Picatout/transistor-tester/transistor-tester.sch

## KiCad design transistor-tester.sch (2013-03-15)

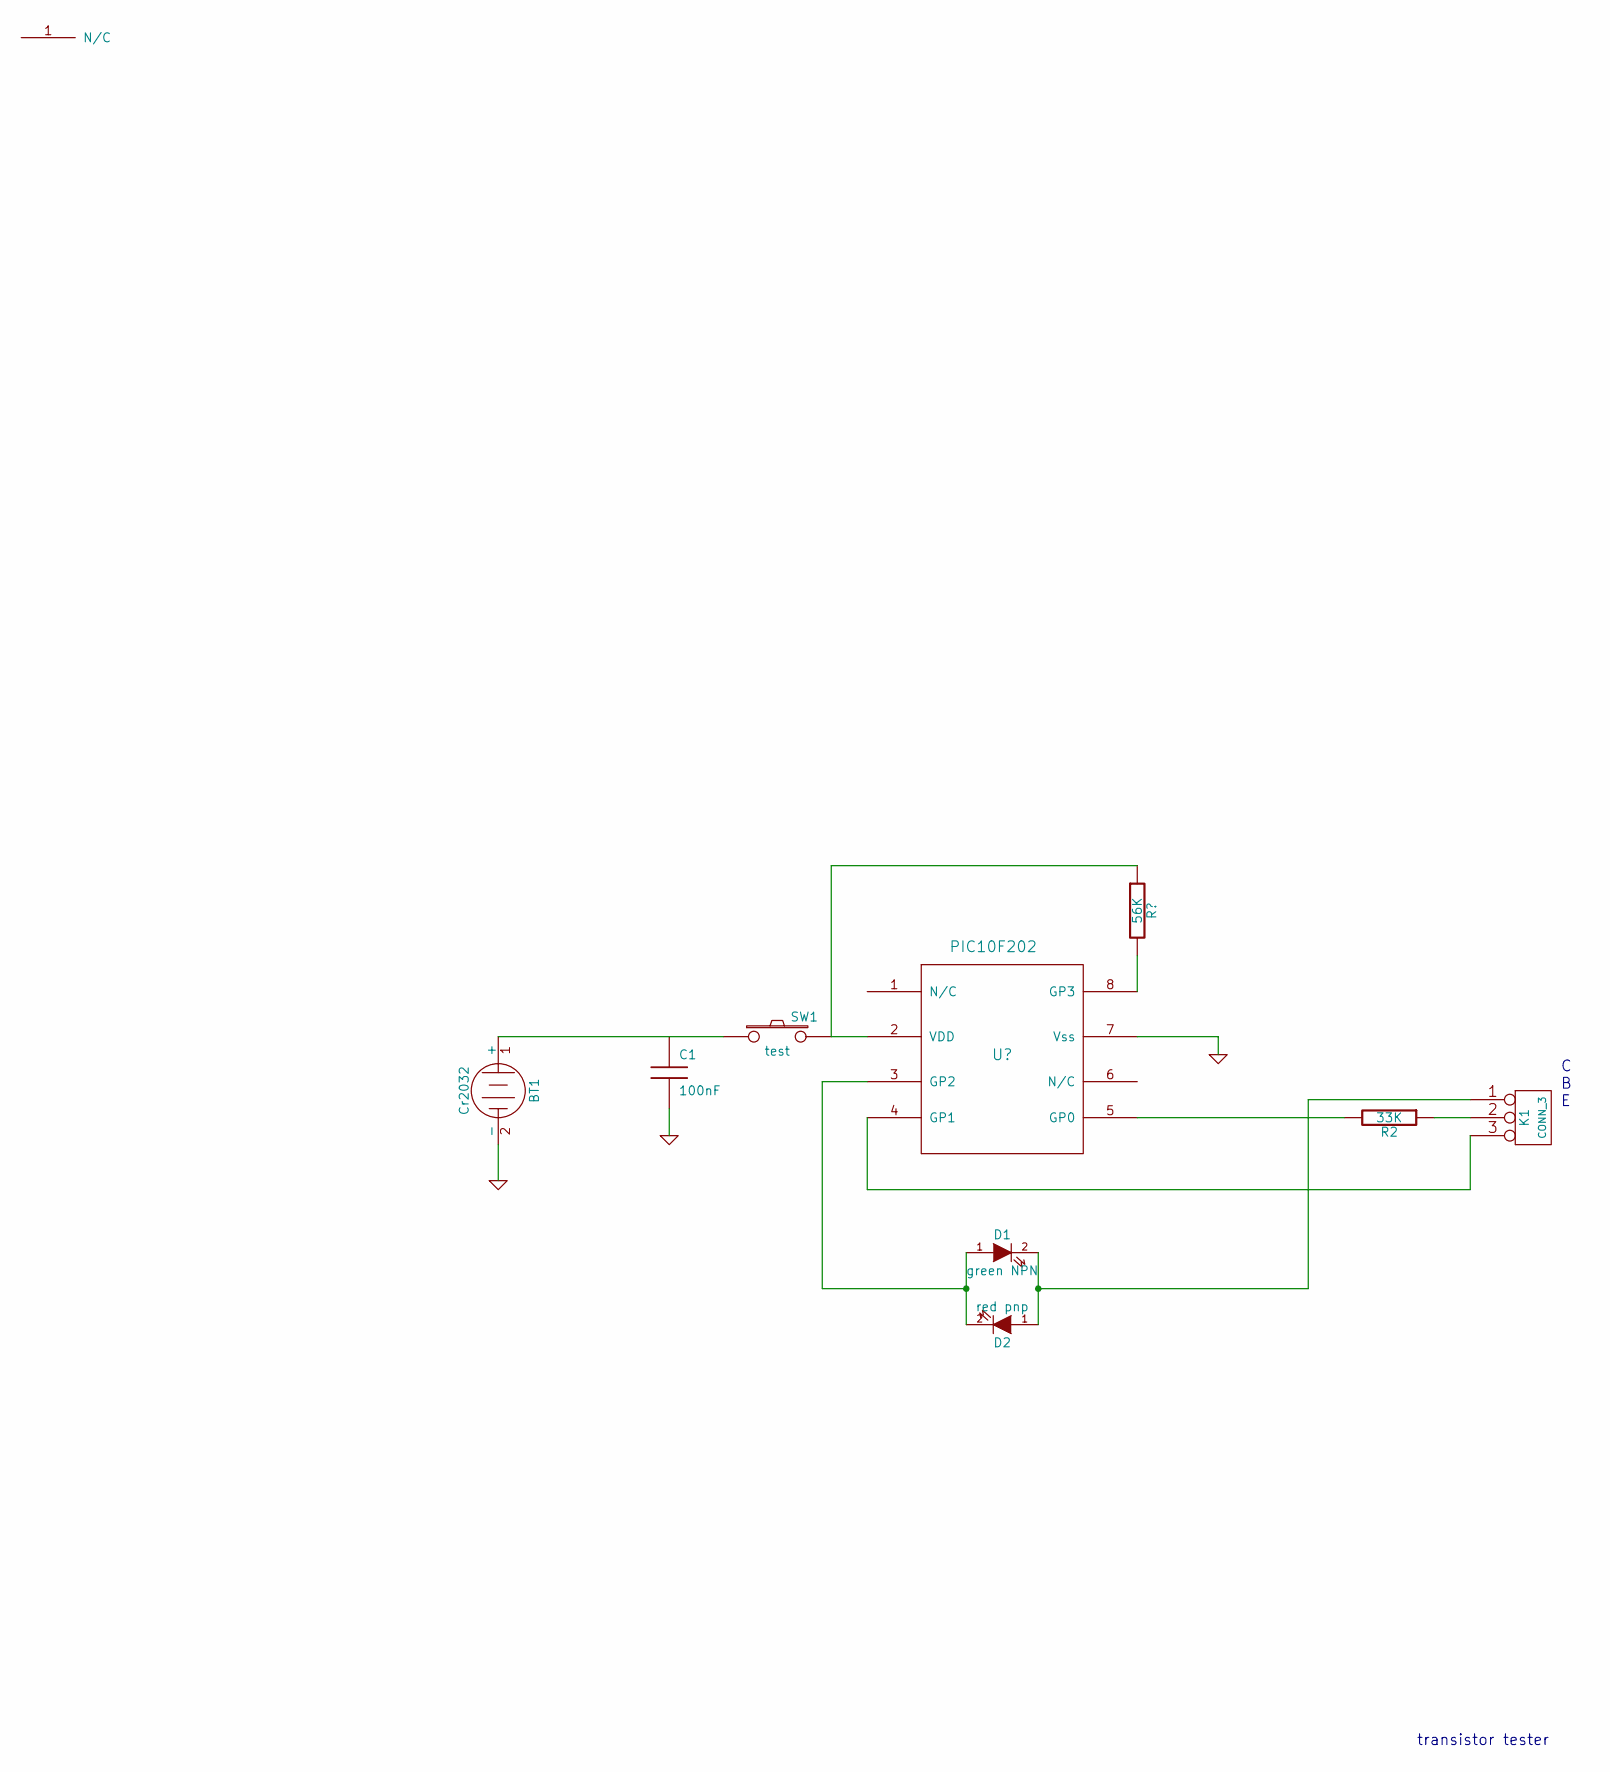
[picture p2: schematic transistor-tester.sch]

Parts:
BT1: Cr2032
C1: 100nF
D1: green NPN
D2: red pnp
K1: CONN_3
R2: 33K
SW1: test

Connections:
GND: BT1.2 (-), C1.2
unnamed: BT1.1 (+), SW1.1
unnamed: D1.1 (A), D2.2 (K)
unnamed: D1.2 (K), D2.1 (A), K1.1
unnamed: K1.2 (PM), R2.1

Notes on the sheet:
C B E
transistor tester
